AliHamzeh2002/Computer-Architecture-Lab/imgs/id_modelsim.png

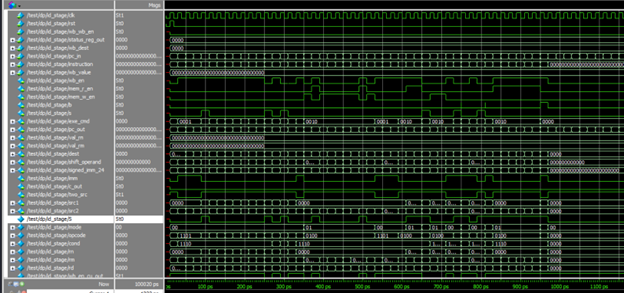
imgs/id_modelsim.png
