AliHamzeh2002/Computer-Architecture-Lab/imgs/modelsim_forwarding.png

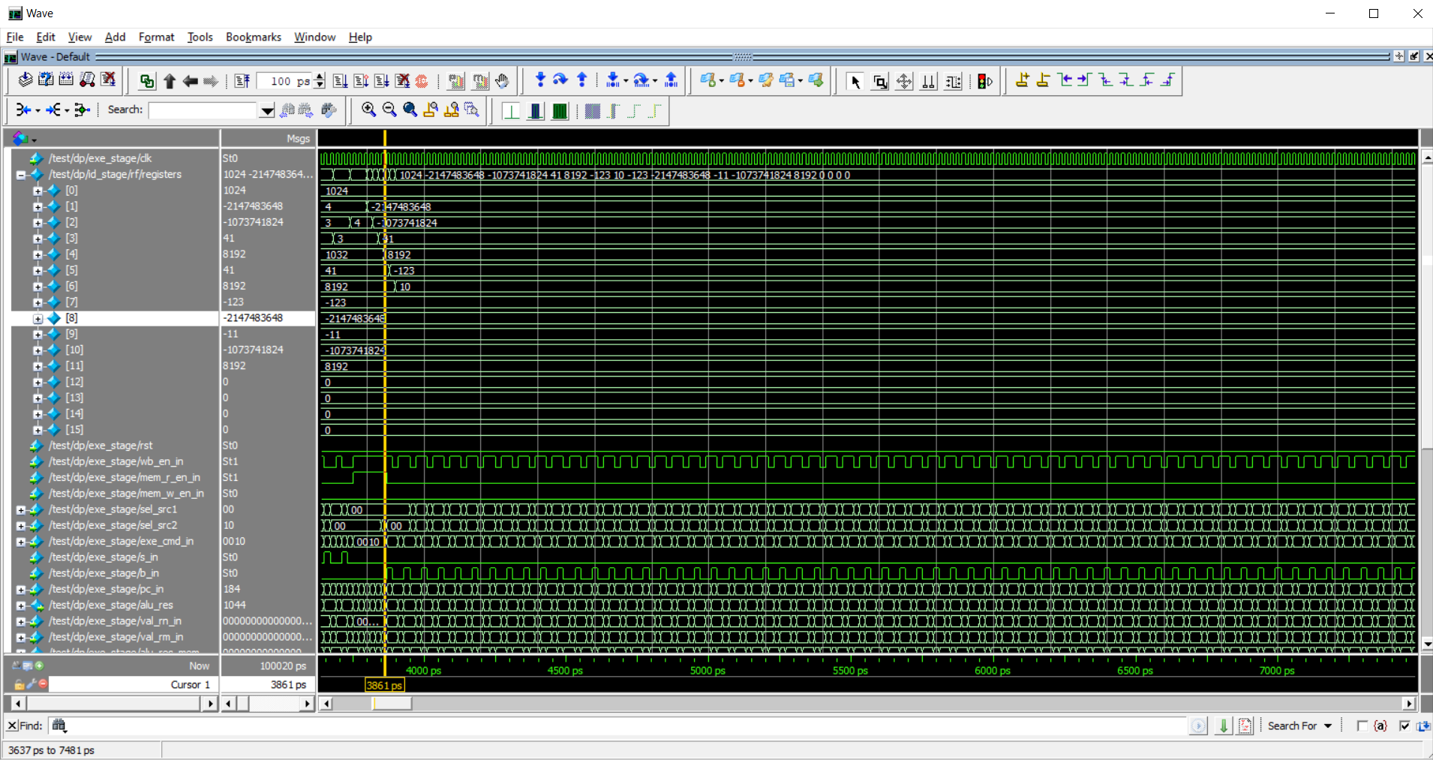
imgs/modelsim_forwarding.png
