AliHamzeh2002/Computer-Architecture-Lab/imgs/modelsim_noforwarding.png

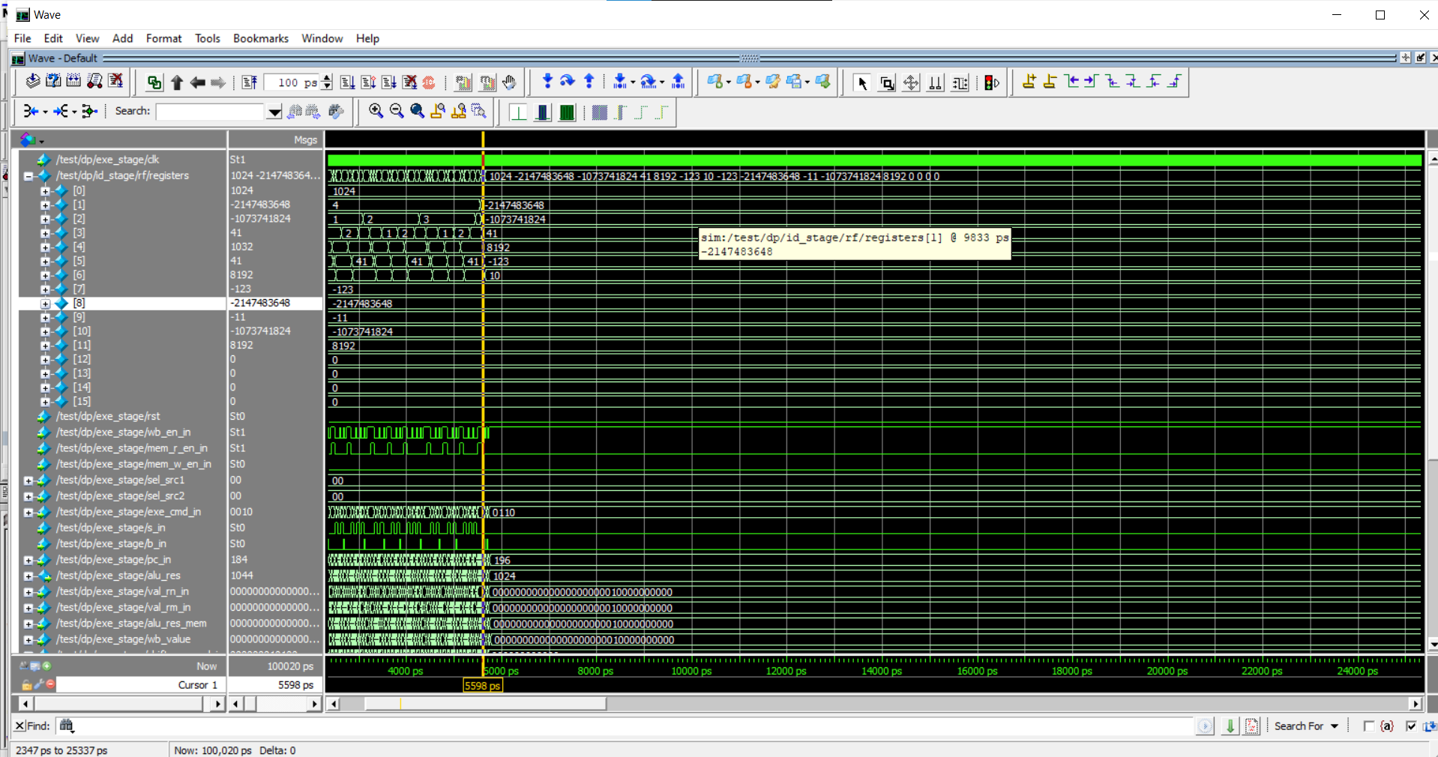
imgs/modelsim_noforwarding.png
