AliHamzeh2002/Computer-Architecture-Lab/imgs/quartus_ARM.png

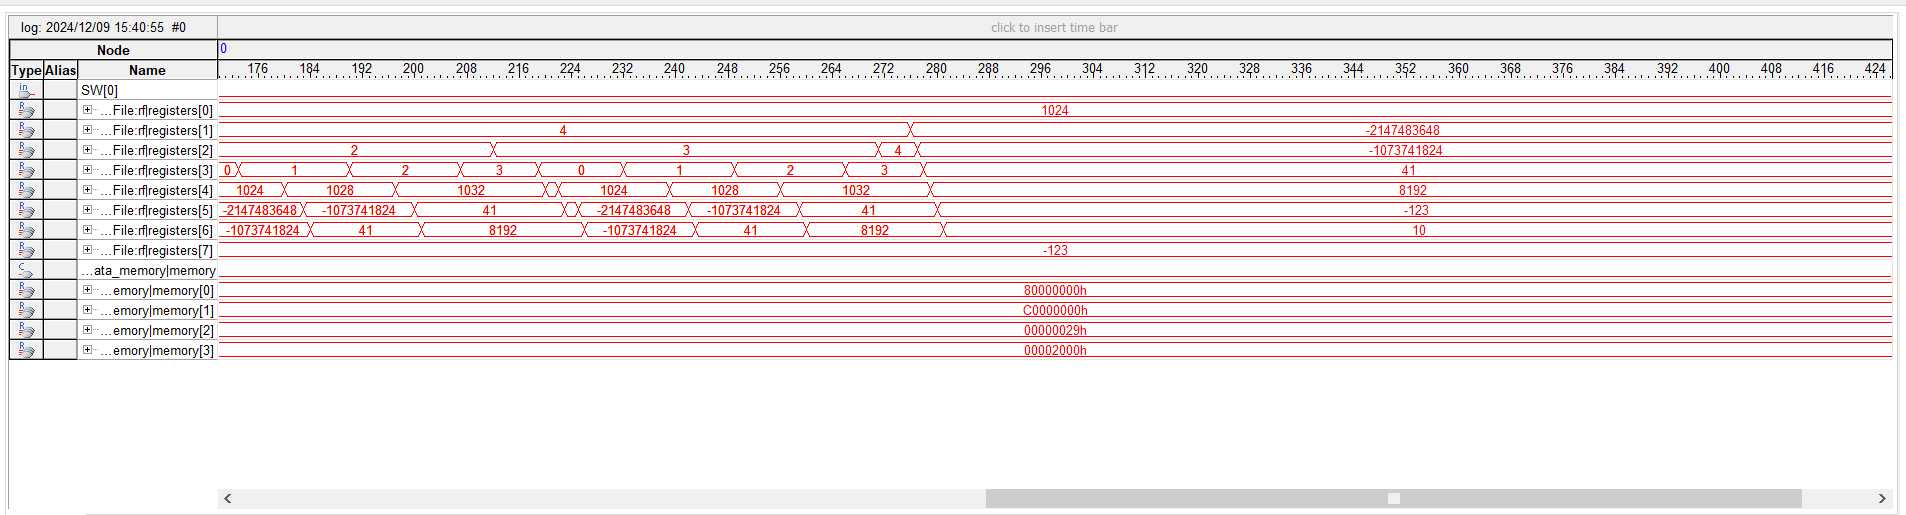
imgs/quartus_ARM.png
