AliHamzeh2002/Computer-Architecture-Lab/imgs/sram_idl.png

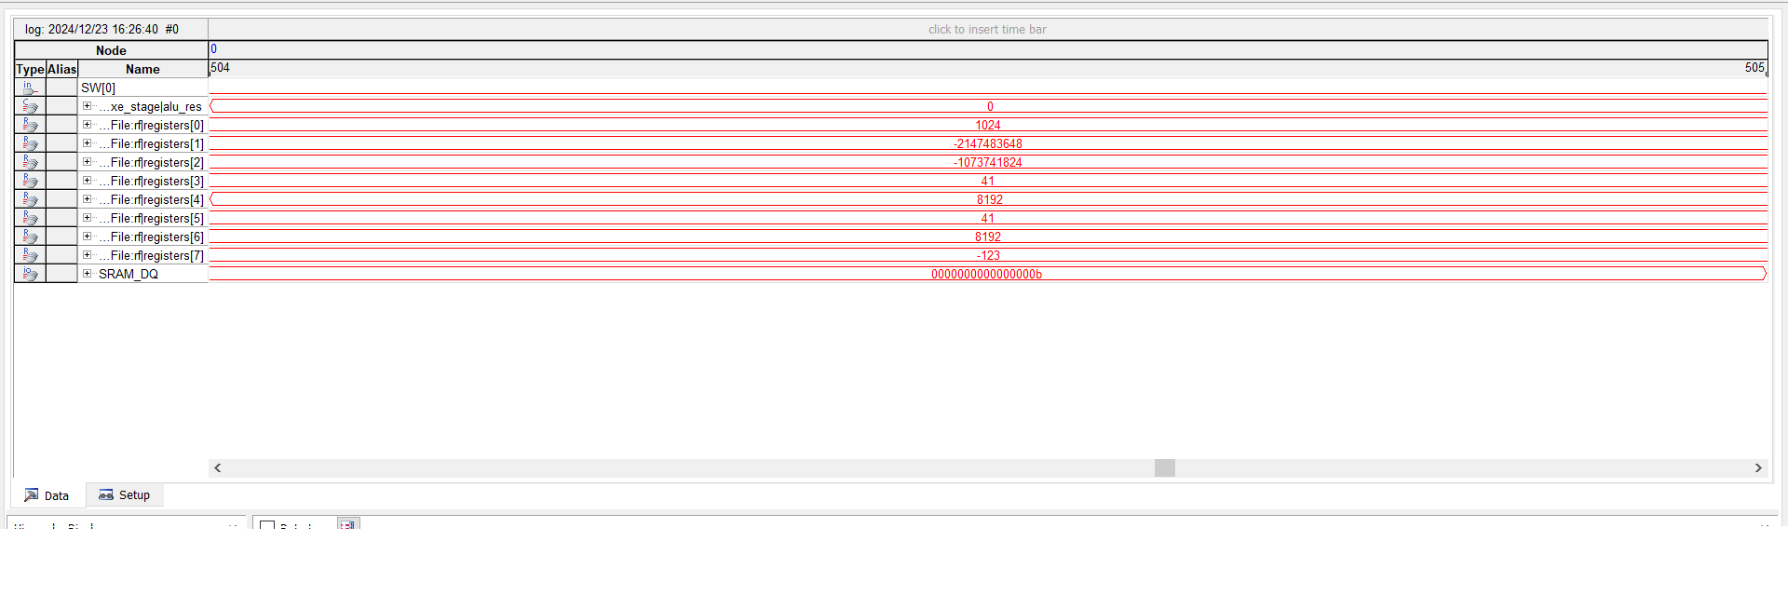
imgs/sram_idl.png
