AliHamzeh2002/Computer-Architecture-Lab/imgs/sram_low_read.png

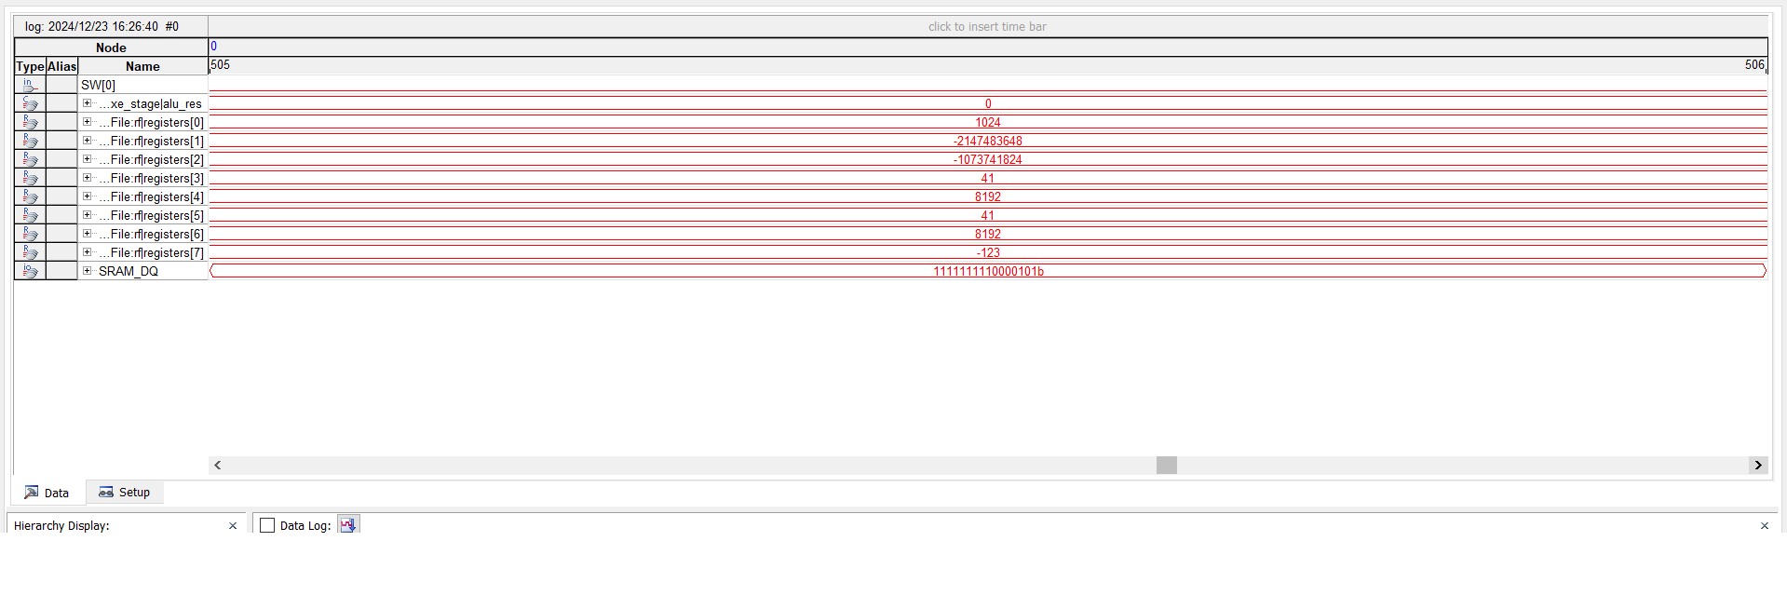
imgs/sram_low_read.png
