AliHamzeh2002/Computer-Architecture-Lab/imgs/sram_modelsim.png

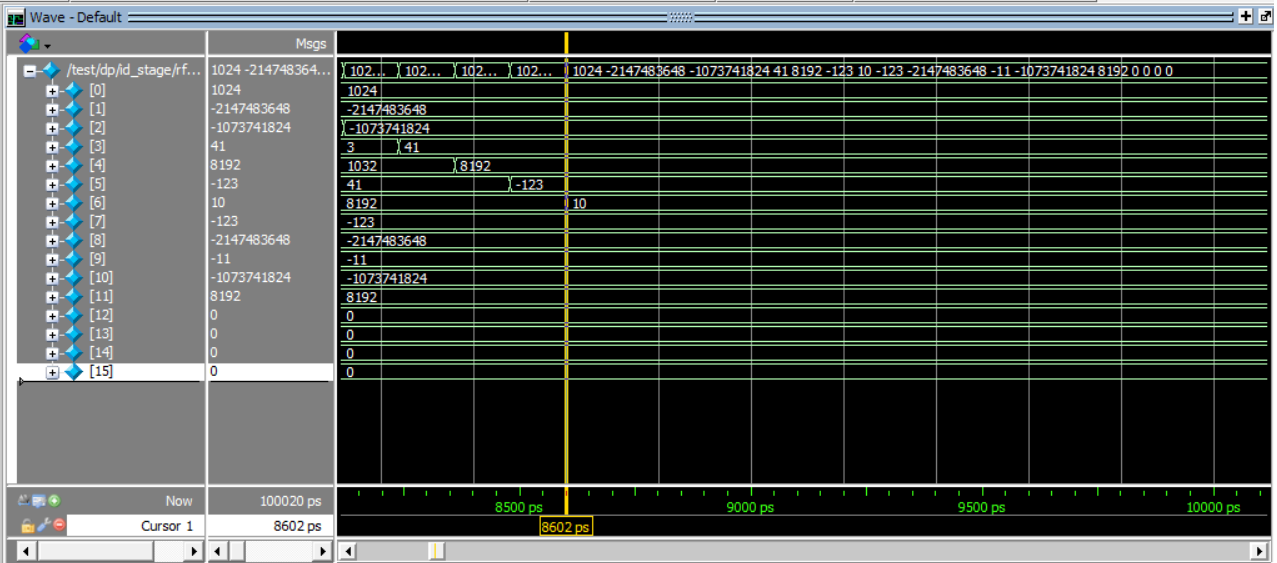
imgs/sram_modelsim.png
