AliHamzeh2002/Computer-Architecture-Lab/imgs/sram_result_in_rf.png

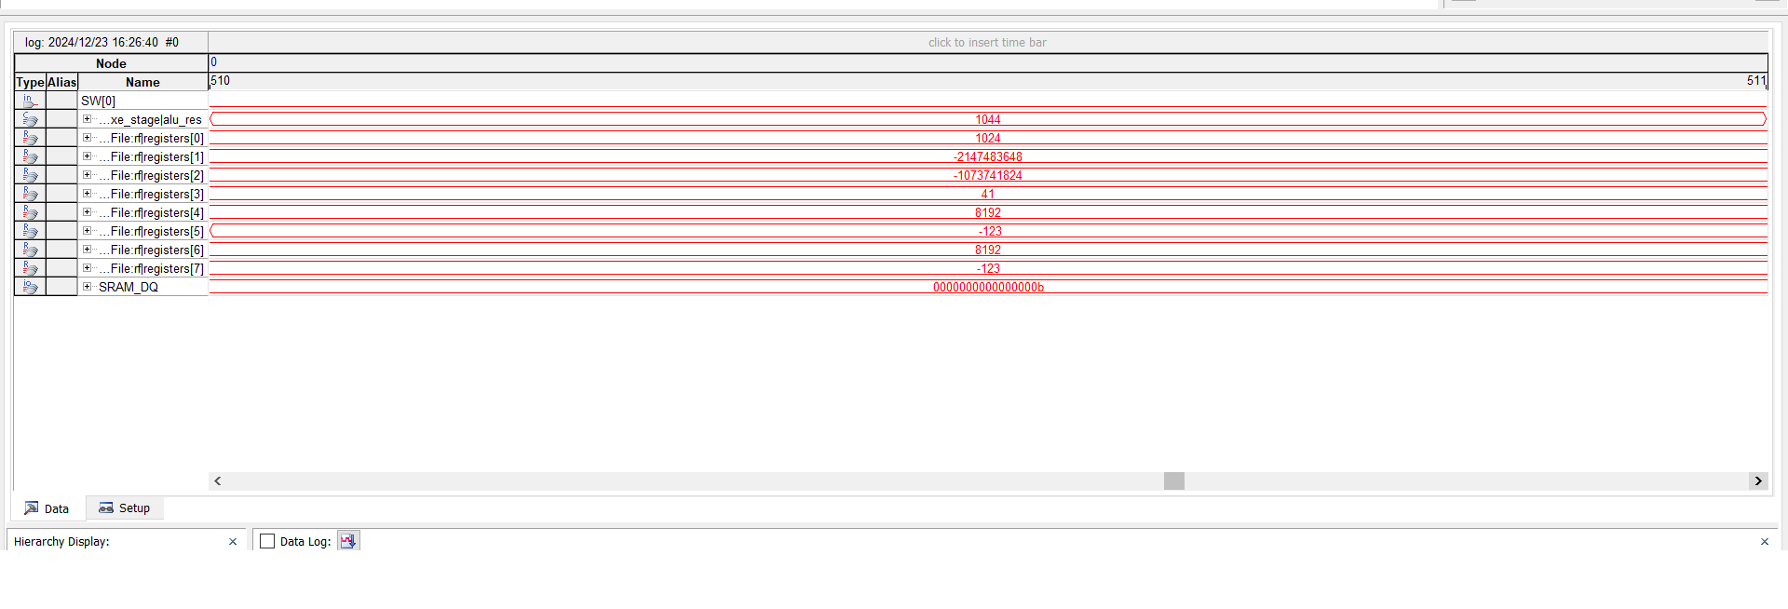
imgs/sram_result_in_rf.png
