AliHamzeh2002/Computer-Architecture-Lab/src/Exe-stage/exe_stage_reg.v

module ExeStageReg (
    input clk, rst, freeze,
    input mem_w_en_in, mem_r_en_in, wb_en_in,
    input [31:0] alu_res_in,
    input [31:0] val_rm_in,
    input [3:0] dest_in,

    output reg mem_w_en_out, mem_r_en_out, wb_en_out,
    output reg [31:0] alu_res_out,
    output reg [31:0] val_rm_out,
    output reg [3:0] dest_out

);
    always @(posedge clk, posedge rst) begin
        if (rst) begin
            mem_r_en_out <= 0;
            wb_en_out <= 0;
            alu_res_out <= 0;
            val_rm_out <= 0;
            dest_out <= 0;
            mem_w_en_out <= 0;
        end else if (~freeze) begin
            mem_r_en_out <= mem_r_en_in;
            wb_en_out <= wb_en_in;
            alu_res_out <= alu_res_in;
            val_rm_out <= val_rm_in;
            dest_out <= dest_in;
            mem_w_en_out <= mem_w_en_in;
        end
    end
endmodule
