AliHamzeh2002/Computer-Architecture-Lab/src/Mem-stage/data_memory.v

module DataMemory (
    input clk,
    input rst,
    input mem_w_en,
    input mem_r_en,
    input [31:0] alu_res,
    input [31:0] val_rm,
    output [31:0] out 
);
    
    reg [31:0] memory [0:63];

    wire [31:0] address = alu_res - 32'd1024;
    wire [31:0] final_address = {2'b00, address[31:2]};

    integer i;

    always @(posedge clk, posedge rst) begin
        if (rst) begin
            for (i = 0; i < 64; i = i + 1) begin
                memory[i] <= 32'b0;
            end
        end 
        else if(mem_w_en) begin
            memory[final_address] <= val_rm;
        end
        else;
    end

    assign out = (mem_r_en) ? memory[final_address] : 32'b0;

    // always @(mem_r_en, final_address) begin
    //     if(mem_r_en) begin
    //         out = memory[final_address];
    //     end
    // end
        
endmodule
