AliHamzeh2002/Computer-Architecture-Lab/src/IF-stage/pc.v

module ProgramCounter (
    input clk, rst, freeze,
    input [31:0] pc_in,
    output reg [31:0] pc_out
);
    always @(posedge clk, posedge rst) begin
        if (rst) begin
            pc_out <= 32'h0;
        end else if (!freeze) begin
            pc_out <= pc_in;
        end
    end
    
endmodule
